Andrew-Palmertree/BlackBeard-System/Face_Recognition/Andrew/Andrew_cropped/cascade_images13_5.jpg

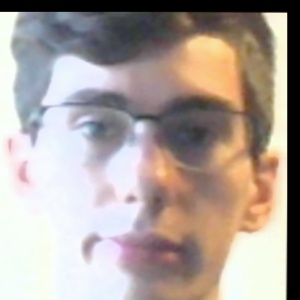
Face_Recognition/Andrew/Andrew_cropped/cascade_images13_5.jpg
