Andrew-Palmertree/BlackBeard-System/Face_Recognition/Andrew/Andrew_cropped/cascade_images13_9.jpg

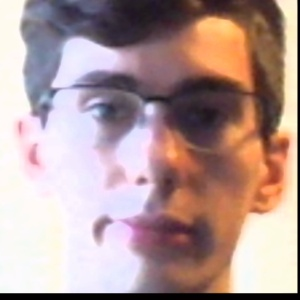
Face_Recognition/Andrew/Andrew_cropped/cascade_images13_9.jpg
