Andrew-Palmertree/BlackBeard-System/Face_Recognition/Andrew/Andrew_cropped/cascade_images20_38.jpg

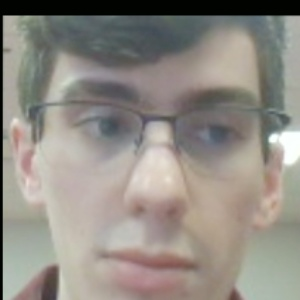
Face_Recognition/Andrew/Andrew_cropped/cascade_images20_38.jpg
