Andrew-Palmertree/BlackBeard-System/Face_Recognition/Andrew/Andrew_cropped/cascade_images43_39.jpg

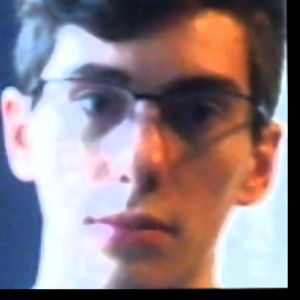
Face_Recognition/Andrew/Andrew_cropped/cascade_images43_39.jpg
