Andrew-Palmertree/BlackBeard-System/Face_Recognition/Andrew/Andrew_cropped/cascade_images48_41.jpg

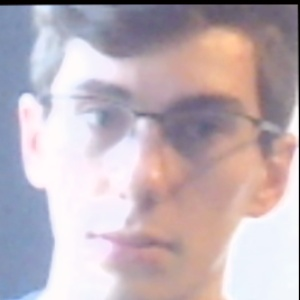
Face_Recognition/Andrew/Andrew_cropped/cascade_images48_41.jpg
