Andrew-Palmertree/BlackBeard-System/Face_Recognition/Andrew/Andrew_cropped/cascade_images61_16.jpg

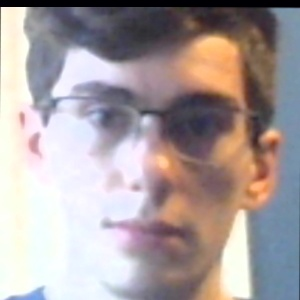
Face_Recognition/Andrew/Andrew_cropped/cascade_images61_16.jpg
