Andrew-Palmertree/BlackBeard-System/Face_Recognition/Andrew/Andrew_cropped/cascade_images74_12.jpg

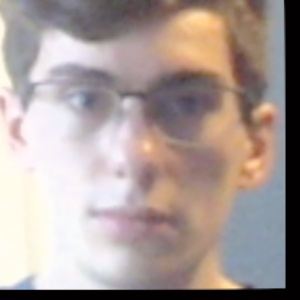
Face_Recognition/Andrew/Andrew_cropped/cascade_images74_12.jpg
