Andrew-Palmertree/BlackBeard-System/Face_Recognition/Andrew/Andrew_cropped/cascade_images75_33.jpg

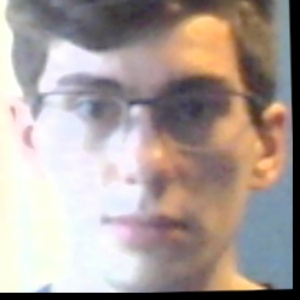
Face_Recognition/Andrew/Andrew_cropped/cascade_images75_33.jpg
