Andrew-Palmertree/BlackBeard-System/Face_Recognition/Andrew/Andrew_cropped/cascade_images76_0.jpg

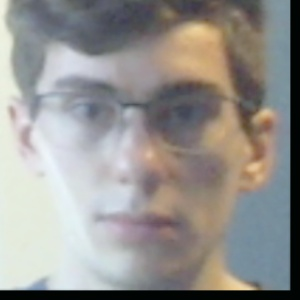
Face_Recognition/Andrew/Andrew_cropped/cascade_images76_0.jpg
