Andrew-Palmertree/BlackBeard-System/Face_Recognition/Andrew/Andrew_cropped/cascade_images77_40.jpg

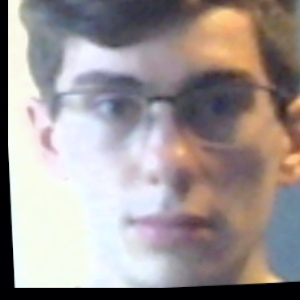
Face_Recognition/Andrew/Andrew_cropped/cascade_images77_40.jpg
