Andrew-Palmertree/BlackBeard-System/Face_Recognition/Andrew/Andrew_cropped/cascade_images79_37.jpg

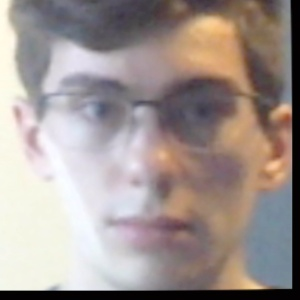
Face_Recognition/Andrew/Andrew_cropped/cascade_images79_37.jpg
