Andrew-Palmertree/BlackBeard-System/Face_Recognition/Andrew/Andrew_cropped/cascade_images80_10.jpg

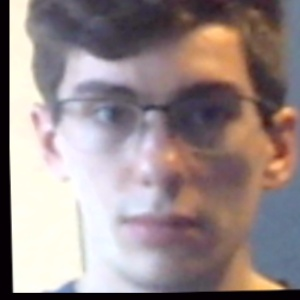
Face_Recognition/Andrew/Andrew_cropped/cascade_images80_10.jpg
