Andrew-Palmertree/BlackBeard-System/Face_Recognition/Andrew/Andrew_cropped/cascade_images80_17.jpg

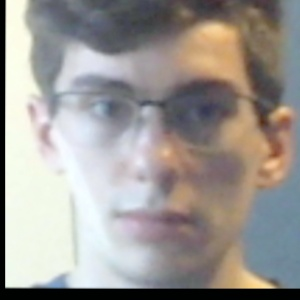
Face_Recognition/Andrew/Andrew_cropped/cascade_images80_17.jpg
