Andrew-Palmertree/BlackBeard-System/Face_Recognition/Andrew/Andrew_cropped/cascade_images80_45.jpg

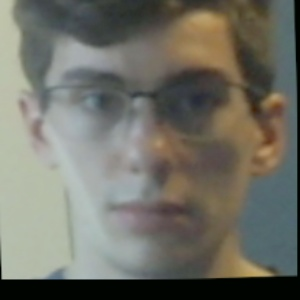
Face_Recognition/Andrew/Andrew_cropped/cascade_images80_45.jpg
