Andrew-Palmertree/BlackBeard-System/Face_Recognition/Andrew/Andrew_cropped/cascade_images82_11.jpg

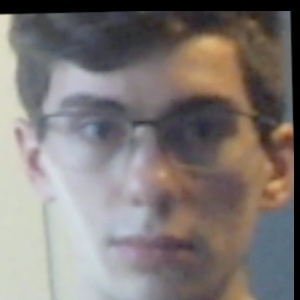
Face_Recognition/Andrew/Andrew_cropped/cascade_images82_11.jpg
