Andrew-Palmertree/BlackBeard-System/Face_Recognition/Andrew/Andrew_cropped/cascade_images93_15.jpg

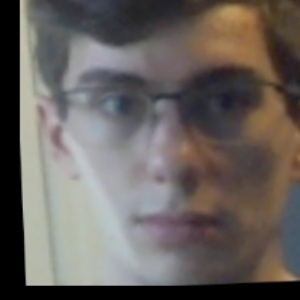
Face_Recognition/Andrew/Andrew_cropped/cascade_images93_15.jpg
