Andrew-Palmertree/BlackBeard-System/Face_Recognition/Andrew/Andrew_cropped/cascade_images101_14.jpg

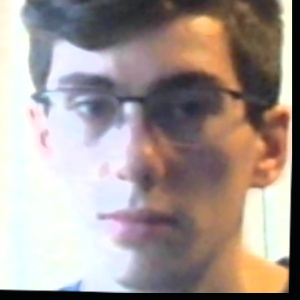
Face_Recognition/Andrew/Andrew_cropped/cascade_images101_14.jpg
