Andrew-Palmertree/BlackBeard-System/Face_Recognition/Andrew/Andrew_images/Andrew_2023-10-12-21-03-56.jpg

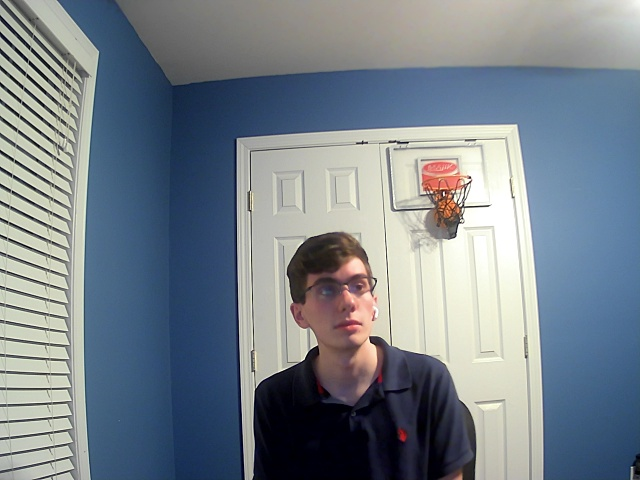
Face_Recognition/Andrew/Andrew_images/Andrew_2023-10-12-21-03-56.jpg
