Andrew-Palmertree/BlackBeard-System/Face_Recognition/Parbin/Parbin_cropped/cascade_images1.jpg

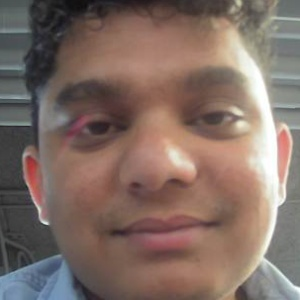
Face_Recognition/Parbin/Parbin_cropped/cascade_images1.jpg
