Andrew-Palmertree/BlackBeard-System/Face_Recognition/Parbin/Parbin_generated/cascade_images102.jpg

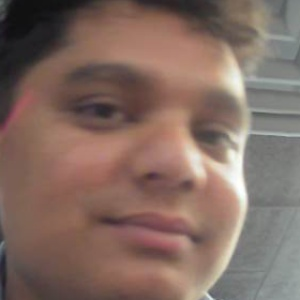
Face_Recognition/Parbin/Parbin_generated/cascade_images102.jpg
