Andrew-Palmertree/BlackBeard-System/Face_Recognition/pubfig/train/Parbin/cascade_images1_59.jpg

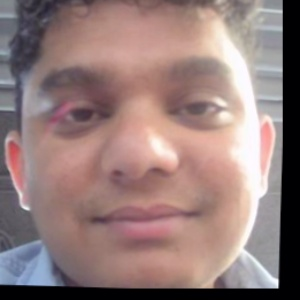
Face_Recognition/pubfig/train/Parbin/cascade_images1_59.jpg
