Andrew-Palmertree/BlackBeard-System/Face_Recognition/pubfig/train/Parbin/cascade_images3_16.jpg

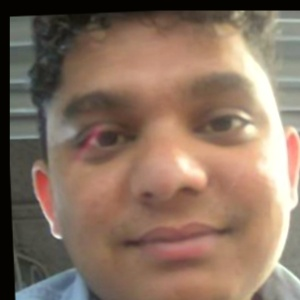
Face_Recognition/pubfig/train/Parbin/cascade_images3_16.jpg
