Andrew-Palmertree/BlackBeard-System/Face_Recognition/pubfig/train/Parbin/cascade_images5_31.jpg

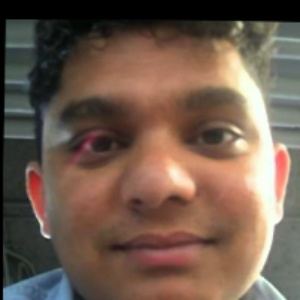
Face_Recognition/pubfig/train/Parbin/cascade_images5_31.jpg
