Andrew-Palmertree/BlackBeard-System/Face_Recognition/pubfig/train/Parbin/cascade_images6_12.jpg

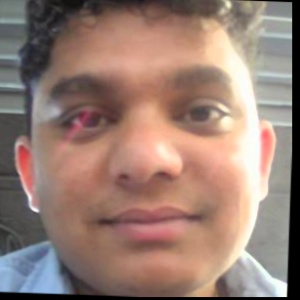
Face_Recognition/pubfig/train/Parbin/cascade_images6_12.jpg
