Andrew-Palmertree/BlackBeard-System/Face_Recognition/pubfig/train/Parbin/cascade_images6_21.jpg

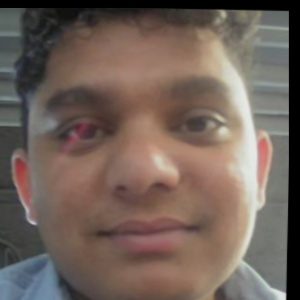
Face_Recognition/pubfig/train/Parbin/cascade_images6_21.jpg
