Andrew-Palmertree/BlackBeard-System/Face_Recognition/pubfig/train/Parbin/cascade_images7_41.jpg

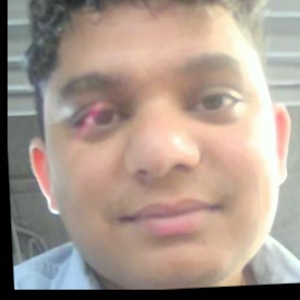
Face_Recognition/pubfig/train/Parbin/cascade_images7_41.jpg
