Andrew-Palmertree/BlackBeard-System/Face_Recognition/pubfig/train/Parbin/cascade_images8_28.jpg

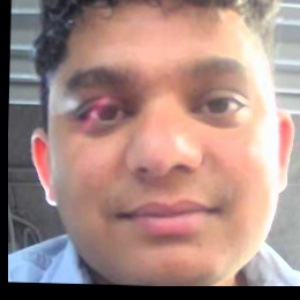
Face_Recognition/pubfig/train/Parbin/cascade_images8_28.jpg
