Andrew-Palmertree/BlackBeard-System/Face_Recognition/pubfig/train/Parbin/cascade_images9_7.jpg

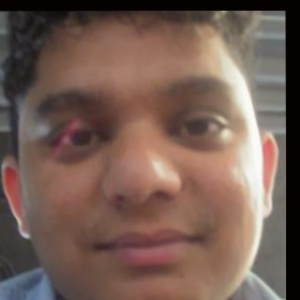
Face_Recognition/pubfig/train/Parbin/cascade_images9_7.jpg
