Andrew-Palmertree/BlackBeard-System/Face_Recognition/pubfig/train/Parbin/cascade_images9_32.jpg

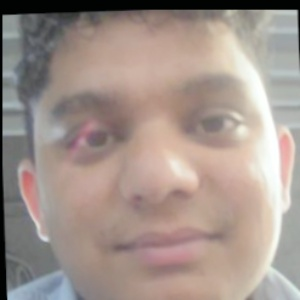
Face_Recognition/pubfig/train/Parbin/cascade_images9_32.jpg
