Andrew-Palmertree/BlackBeard-System/Face_Recognition/pubfig/train/Parbin/cascade_images10_56.jpg

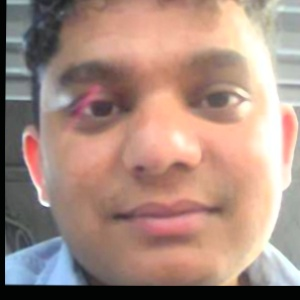
Face_Recognition/pubfig/train/Parbin/cascade_images10_56.jpg
