Andrew-Palmertree/BlackBeard-System/Face_Recognition/pubfig/train/Parbin/cascade_images11_8.jpg

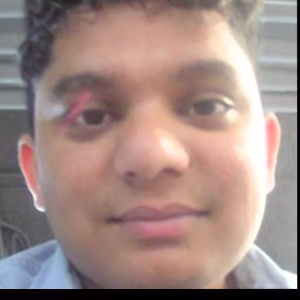
Face_Recognition/pubfig/train/Parbin/cascade_images11_8.jpg
