Andrew-Palmertree/BlackBeard-System/Face_Recognition/pubfig/train/Parbin/cascade_images11_34.jpg

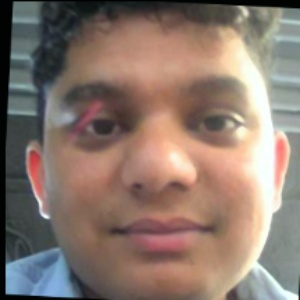
Face_Recognition/pubfig/train/Parbin/cascade_images11_34.jpg
