Andrew-Palmertree/BlackBeard-System/Face_Recognition/pubfig/train/Parbin/cascade_images11_48.jpg

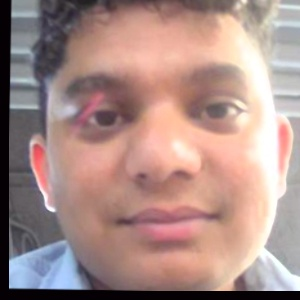
Face_Recognition/pubfig/train/Parbin/cascade_images11_48.jpg
