Andrew-Palmertree/BlackBeard-System/Face_Recognition/pubfig/train/Parbin/cascade_images12_2.jpg

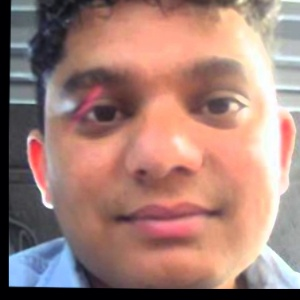
Face_Recognition/pubfig/train/Parbin/cascade_images12_2.jpg
