Andrew-Palmertree/BlackBeard-System/Face_Recognition/pubfig/train/Unknown/995a822699ca4232851d1a02c32db64f-74665449.jpg

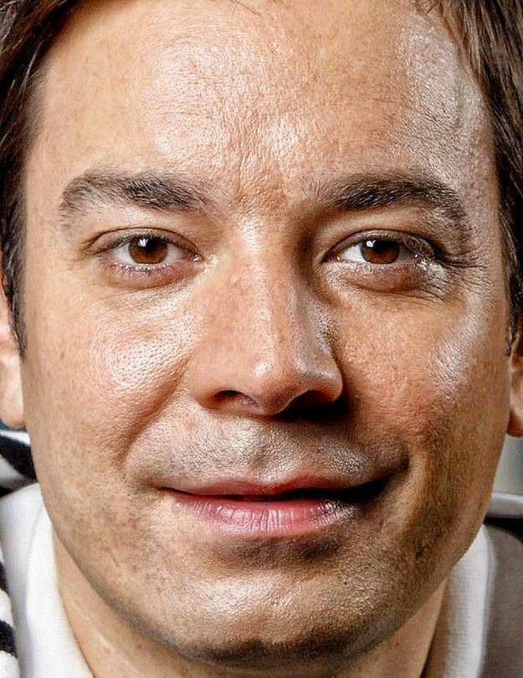
Face_Recognition/pubfig/train/Unknown/995a822699ca4232851d1a02c32db64f-74665449.jpg
