Andrew-Palmertree/BlackBeard-System/Face_Recognition/pubfig/train/Unknown/2592x3888_px_Amateur_brunette_closeup_face_Glasses_smiling-558851-2522647711.jpg

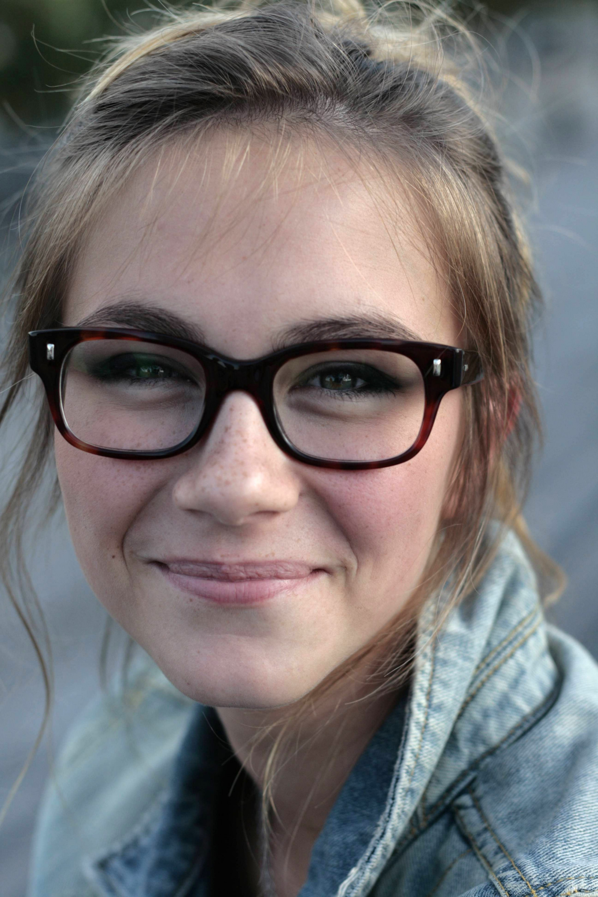
Face_Recognition/pubfig/train/Unknown/2592x3888_px_Amateur_brunette_closeup_face_Glasses_smiling-558851-2522647711.jpg
