Andrew-Palmertree/BlackBeard-System/Face_Recognition/pubfig/train/Unknown/6593056-216999991.jpg

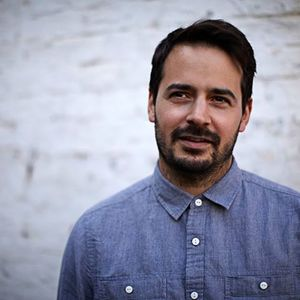
Face_Recognition/pubfig/train/Unknown/6593056-216999991.jpg
