Andrew-Palmertree/BlackBeard-System/Face_Recognition/pubfig/train/Unknown/ABS_Marion-Berry-2048x1367-1784466016.jpg

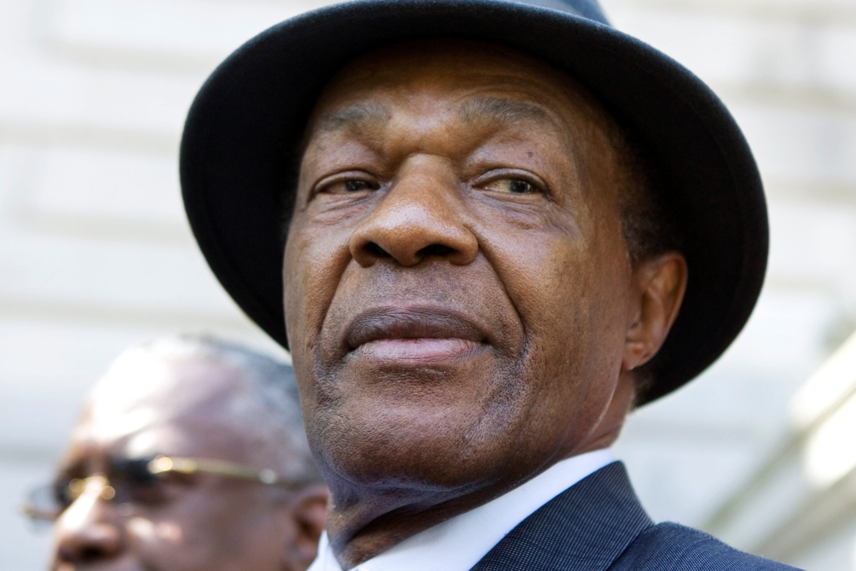
Face_Recognition/pubfig/train/Unknown/ABS_Marion-Berry-2048x1367-1784466016.jpg
