Andrew-Palmertree/BlackBeard-System/Face_Recognition/pubfig/train/Unknown/hebrew-man-1630919685.jpg

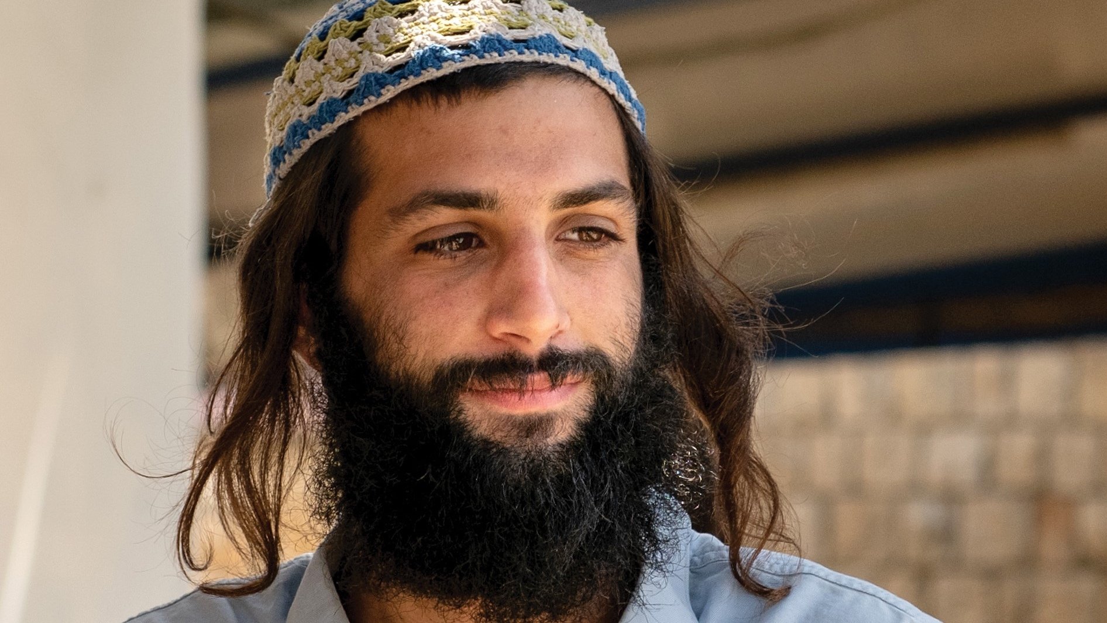
Face_Recognition/pubfig/train/Unknown/hebrew-man-1630919685.jpg
