Andrew-Palmertree/BlackBeard-System/Face_Recognition/pubfig/train/Unknown/image-773013927.jpg

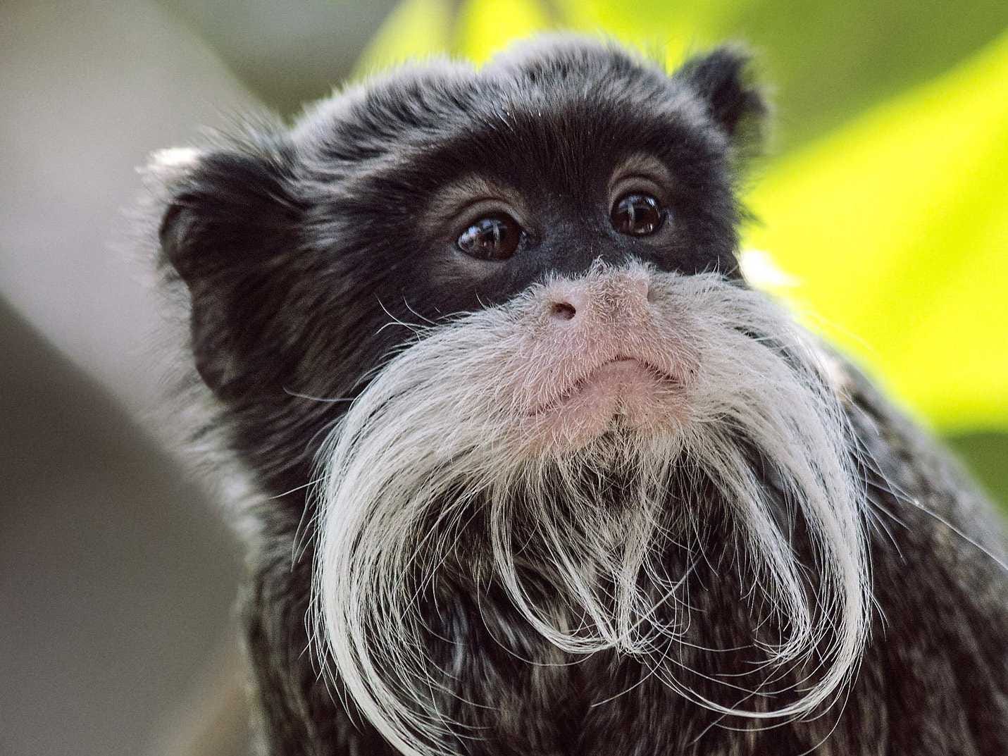
Face_Recognition/pubfig/train/Unknown/image-773013927.jpg
