Andrew-Palmertree/BlackBeard-System/Face_Recognition/pubfig/train/Unknown/pretty-brunette-woman-smiling-wearing-glasses-close-up-portrait-47325780-1562049896.jpg

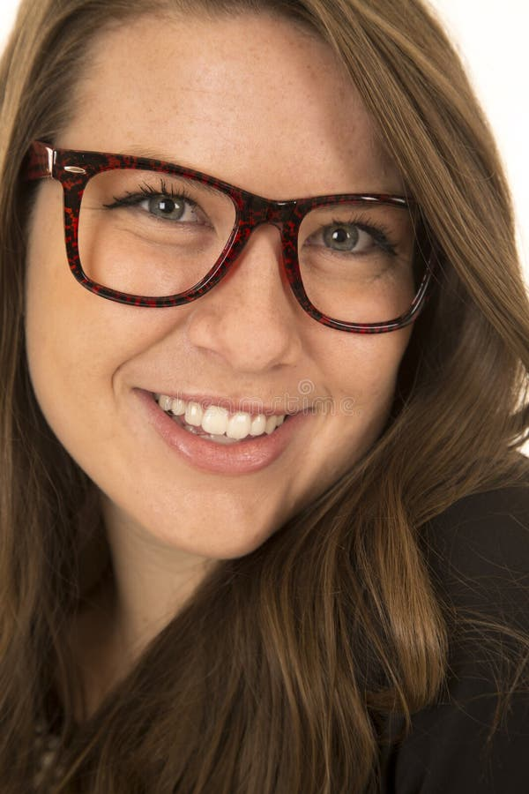
Face_Recognition/pubfig/train/Unknown/pretty-brunette-woman-smiling-wearing-glasses-close-up-portrait-47325780-1562049896.jpg
