Andrew-Palmertree/BlackBeard-System/Face_Recognition/pubfig/train/Unknown/th-85895982.jpg

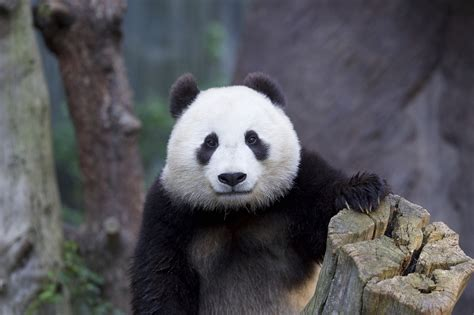
Face_Recognition/pubfig/train/Unknown/th-85895982.jpg
