Andrew-Palmertree/BlackBeard-System/Face_Recognition/pubfig/train/Unknown/th-3168737238.jpg

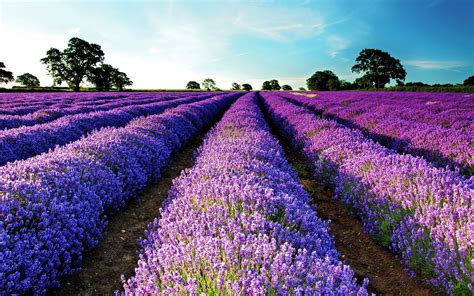
Face_Recognition/pubfig/train/Unknown/th-3168737238.jpg
