Andrew-Palmertree/BlackBeard-System/Face_Recognition/pubfig/train/Unknown/th-3412899006.jpg

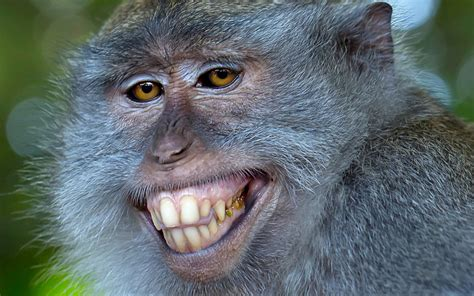
Face_Recognition/pubfig/train/Unknown/th-3412899006.jpg
