Andrew-Palmertree/BlackBeard-System/Face_Recognition/pubfig/train/Unknown/woman-with-glasses-touching-head-675256116.jpg

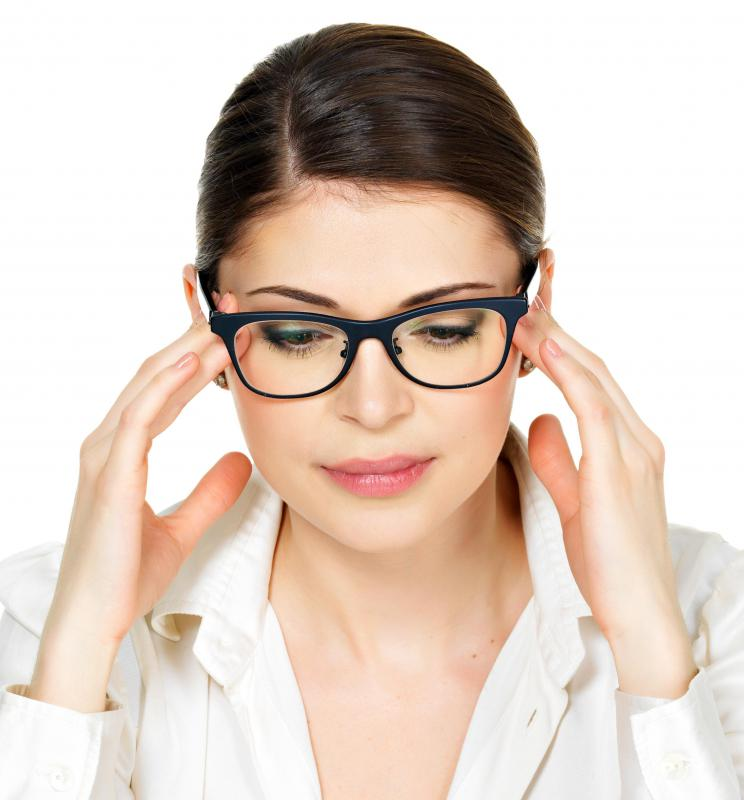
Face_Recognition/pubfig/train/Unknown/woman-with-glasses-touching-head-675256116.jpg
