Andrew-Palmertree/BlackBeard-System/Face_Recognition/pubfig/train/Will/cascade_images1_5.jpg

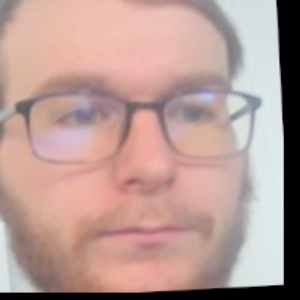
Face_Recognition/pubfig/train/Will/cascade_images1_5.jpg
