Andrew-Palmertree/BlackBeard-System/Face_Recognition/pubfig/train/Will/cascade_images2_21.jpg

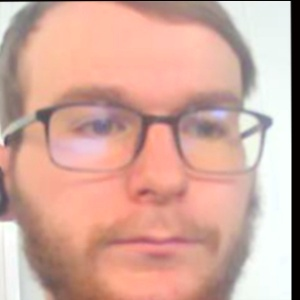
Face_Recognition/pubfig/train/Will/cascade_images2_21.jpg
