Andrew-Palmertree/BlackBeard-System/Face_Recognition/pubfig/train/Will/cascade_images3_22.jpg

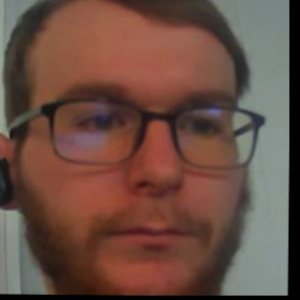
Face_Recognition/pubfig/train/Will/cascade_images3_22.jpg
