Andrew-Palmertree/BlackBeard-System/Face_Recognition/pubfig/train/Will/cascade_images3_36.jpg

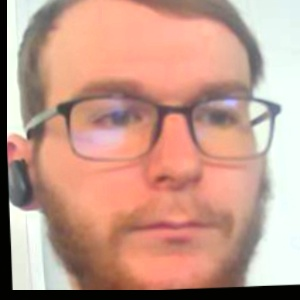
Face_Recognition/pubfig/train/Will/cascade_images3_36.jpg
