Andrew-Palmertree/BlackBeard-System/Face_Recognition/pubfig/train/Will/cascade_images5_12.jpg

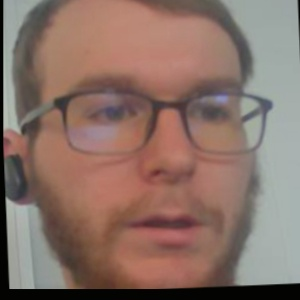
Face_Recognition/pubfig/train/Will/cascade_images5_12.jpg
