Andrew-Palmertree/BlackBeard-System/Face_Recognition/pubfig/train/Will/cascade_images5_25.jpg

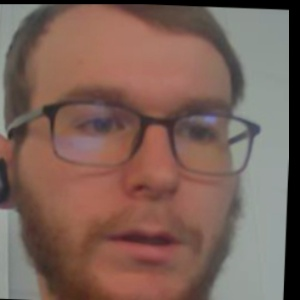
Face_Recognition/pubfig/train/Will/cascade_images5_25.jpg
