Andrew-Palmertree/BlackBeard-System/Face_Recognition/pubfig/train/Will/cascade_images5_50.jpg

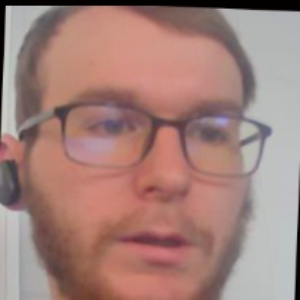
Face_Recognition/pubfig/train/Will/cascade_images5_50.jpg
