Andrew-Palmertree/BlackBeard-System/Face_Recognition/pubfig/train/Will/cascade_images6_38.jpg

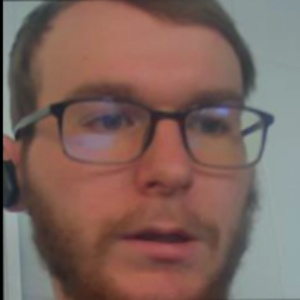
Face_Recognition/pubfig/train/Will/cascade_images6_38.jpg
