Andrew-Palmertree/BlackBeard-System/Face_Recognition/pubfig/train/Will/cascade_images7_56.jpg

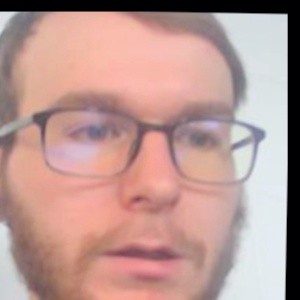
Face_Recognition/pubfig/train/Will/cascade_images7_56.jpg
