Andrew-Palmertree/BlackBeard-System/Face_Recognition/pubfig/train/Will/cascade_images8_20.jpg

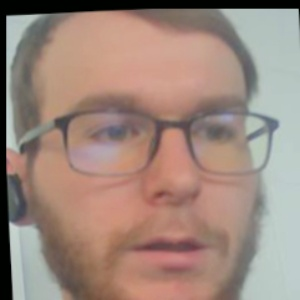
Face_Recognition/pubfig/train/Will/cascade_images8_20.jpg
