Andrew-Palmertree/BlackBeard-System/Face_Recognition/pubfig/train/Will/cascade_images9_23.jpg

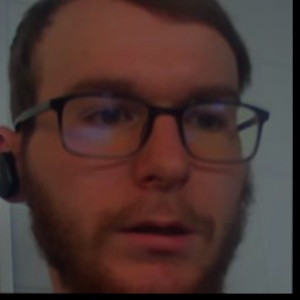
Face_Recognition/pubfig/train/Will/cascade_images9_23.jpg
