Andrew-Palmertree/BlackBeard-System/Face_Recognition/pubfig/train/Will/cascade_images9_53.jpg

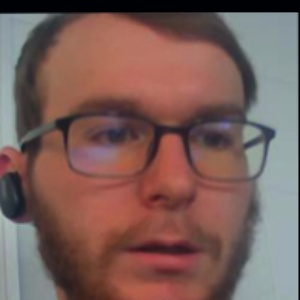
Face_Recognition/pubfig/train/Will/cascade_images9_53.jpg
