Andrew-Palmertree/BlackBeard-System/Face_Recognition/pubfig/train/Will/cascade_images11_4.jpg

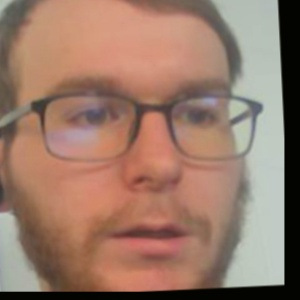
Face_Recognition/pubfig/train/Will/cascade_images11_4.jpg
