Andrew-Palmertree/BlackBeard-System/Face_Recognition/pubfig/train/Will/cascade_images12_9.jpg

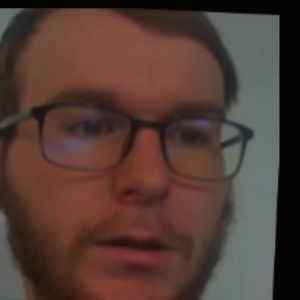
Face_Recognition/pubfig/train/Will/cascade_images12_9.jpg
