Andrew-Palmertree/BlackBeard-System/Face_Recognition/pubfig/train/Will/cascade_images12_48.jpg

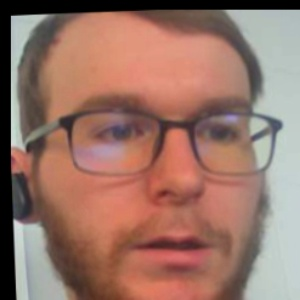
Face_Recognition/pubfig/train/Will/cascade_images12_48.jpg
