Andrew-Palmertree/BlackBeard-System/Face_Recognition/pubfig/train/Will/cascade_images13_31.jpg

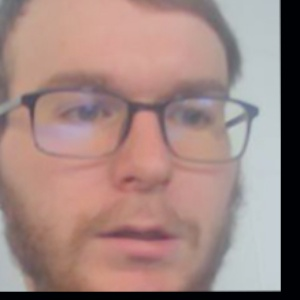
Face_Recognition/pubfig/train/Will/cascade_images13_31.jpg
