Andrew-Palmertree/BlackBeard-System/Face_Recognition/pubfig/train/Will/cascade_images14_7.jpg

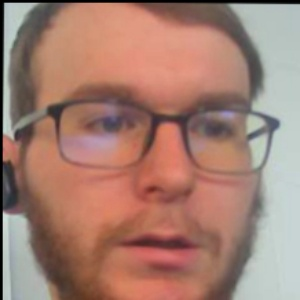
Face_Recognition/pubfig/train/Will/cascade_images14_7.jpg
