Andrew-Palmertree/BlackBeard-System/Face_Recognition/pubfig/train/Will/cascade_images15_37.jpg

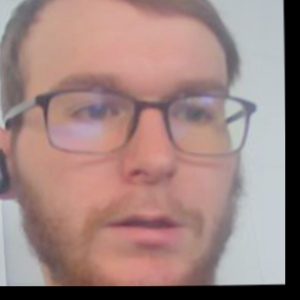
Face_Recognition/pubfig/train/Will/cascade_images15_37.jpg
