Andrew-Palmertree/BlackBeard-System/Face_Recognition/pubfig/train/Will/cascade_images16_32.jpg

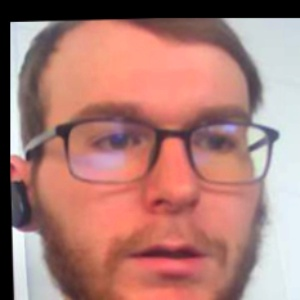
Face_Recognition/pubfig/train/Will/cascade_images16_32.jpg
