Andrew-Palmertree/BlackBeard-System/Face_Recognition/pubfig/train/Will/cascade_images16_44.jpg

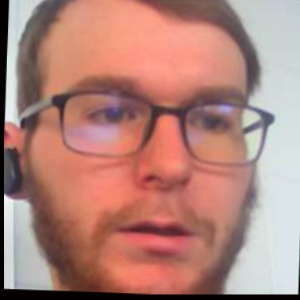
Face_Recognition/pubfig/train/Will/cascade_images16_44.jpg
