Andrew-Palmertree/BlackBeard-System/Face_Recognition/public_images/2.jpg

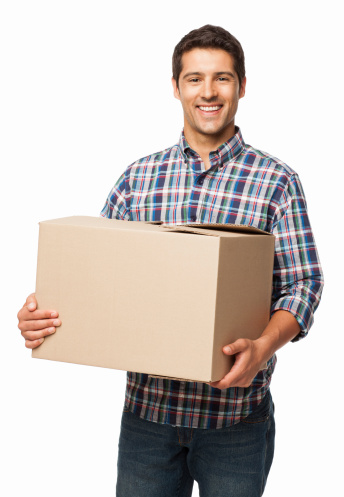
Face_Recognition/public_images/2.jpg
