Andrew-Palmertree/BlackBeard-System/Face_Recognition/Unknown/Unknown_images/202557.jpg

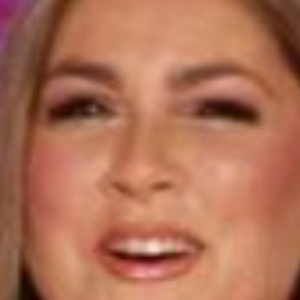
Face_Recognition/Unknown/Unknown_images/202557.jpg
