Andrew-Palmertree/BlackBeard-System/Face_Recognition/Will/Will_cropped/cascade_images1.jpg

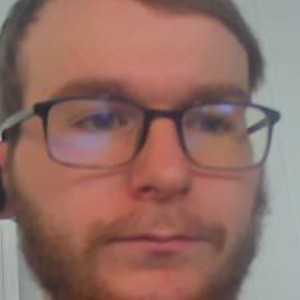
Face_Recognition/Will/Will_cropped/cascade_images1.jpg
