Andrew-Palmertree/BlackBeard-System/Face_Recognition/Will/Will_cropped_backup/cascade_images2.jpg

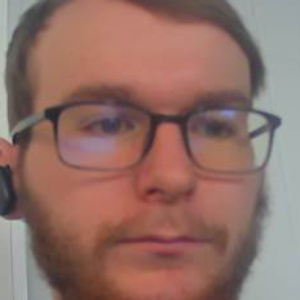
Face_Recognition/Will/Will_cropped_backup/cascade_images2.jpg
