Andrew-Palmertree/BlackBeard-System/Face_Recognition/Will/Will_images/Will_2023-10-17-11-25-39.jpg

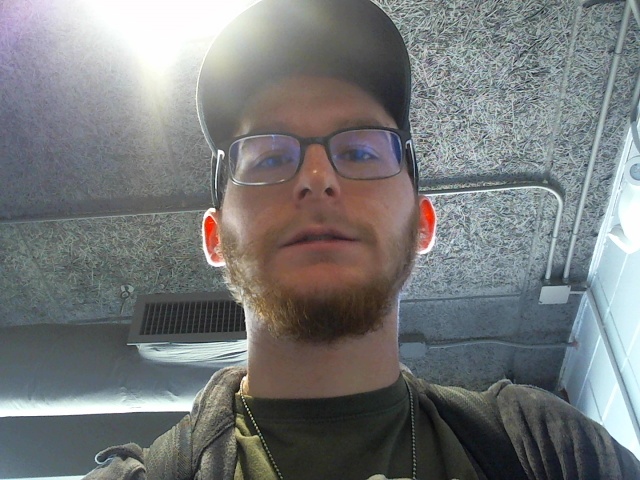
Face_Recognition/Will/Will_images/Will_2023-10-17-11-25-39.jpg
