Andrew-Palmertree/BlackBeard-System/Senior_project/Server/pubfig/train/6-Justin/face_3.png

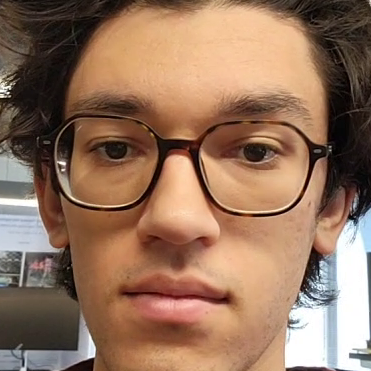
Senior_project/Server/pubfig/train/6-Justin/face_3.png
