Andrew-Palmertree/BlackBeard-System/Senior_project/Server/received_frame.jpg

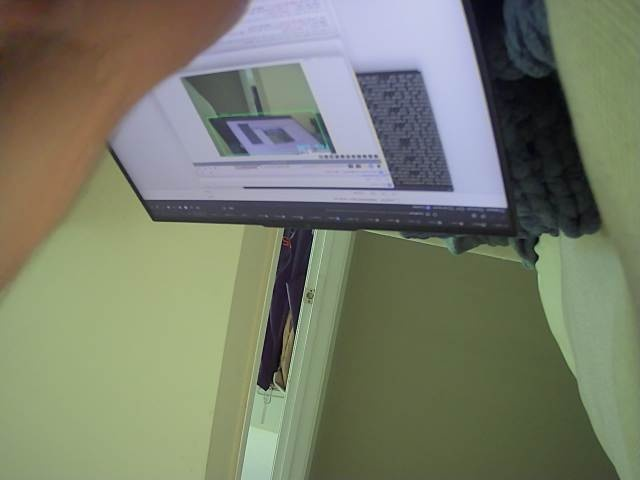
Senior_project/Server/received_frame.jpg
